ErichHeinemann/MiniWI/MINI-WI-ESP32/mini_wi_esp32/MIDI.ino

byte last_channel=0;
byte last_number=0;
byte last_value=0;

// Serial on Pin 16 RX / 17 TX
// 16-Lila
// 17 Blau


// #define MYCHANNEL 0

// void handleNoteOn

/*void MIDI_setup(){
 //  MIDI.begin();
  // Register MIDI-Handlers
  MIDI.setHandleNoteOn( handleNoteOn );
  MIDI.setHandleNoteOff( handleNoteOff );
  MIDI.setHandleControlChange( handleControlChange );
  MIDI.setHandleProgramChange( handleProgramChange );
  MIDI.setHandlePitchBend( handlePitchBend );
  MIDI.setHandleClock( handleClock );
  MIDI.setHandleStart( handleStart );
  MIDI.setHandleStop( handleStop );
  MIDI.setHandleContinue( handleContinue );
  MIDI.setHandleContinue( handleContinue );
}
*/
